shufps/0xaxe/0xaxe/0xaxe.kicad_sch

## KiCad design 0xaxe/0xaxe.kicad_sch (2024-04-14)

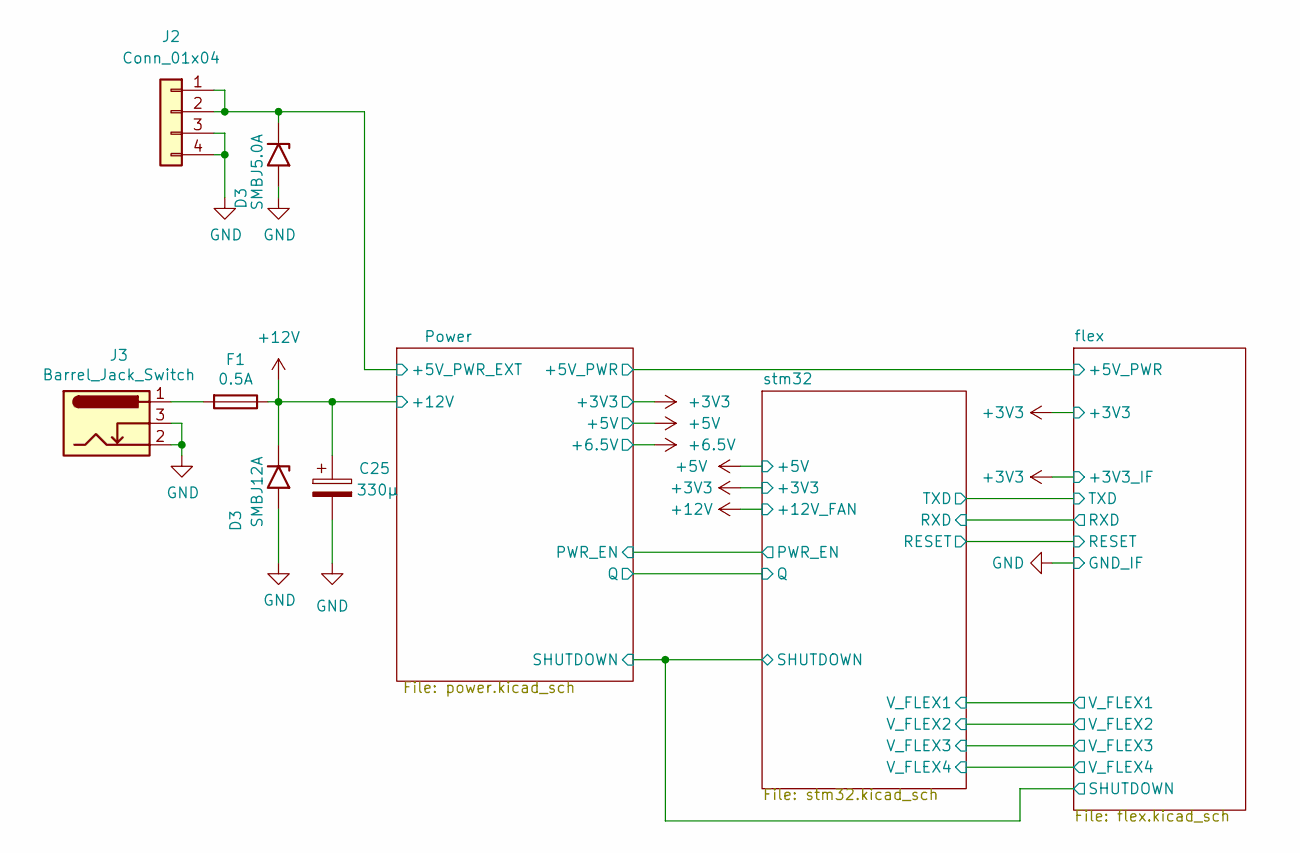
[picture p4: schematic 0xaxe.kicad_sch]

Parts:
C25: 330µ; CP_Elec_8x10
D3: SMBJ12A; D_SMB
F1: 0.5A; fuseholder_littlefuse_blok
J2: Conn_01x04; BARRIER-TERMINAL-ANYTEK-4pol
J3: Barrel_Jack_Switch; BarrelJack_CUI_PJ-102AH_Horizontal

Connections:
+5V_PWR_EXT: D3.1 (A1), J2.1, J2.2
+12V: C25.1, D3.1 (A1), F1.1
GND: C25.2, D3.2 (A2), J2.3, J2.4, J3.2, J3.3
unnamed: F1.2, J3.1
