shufps/0xaxe/0xaxe/flex1.kicad_sch

## KiCad design 0xaxe/flex1.kicad_sch (2024-04-14)

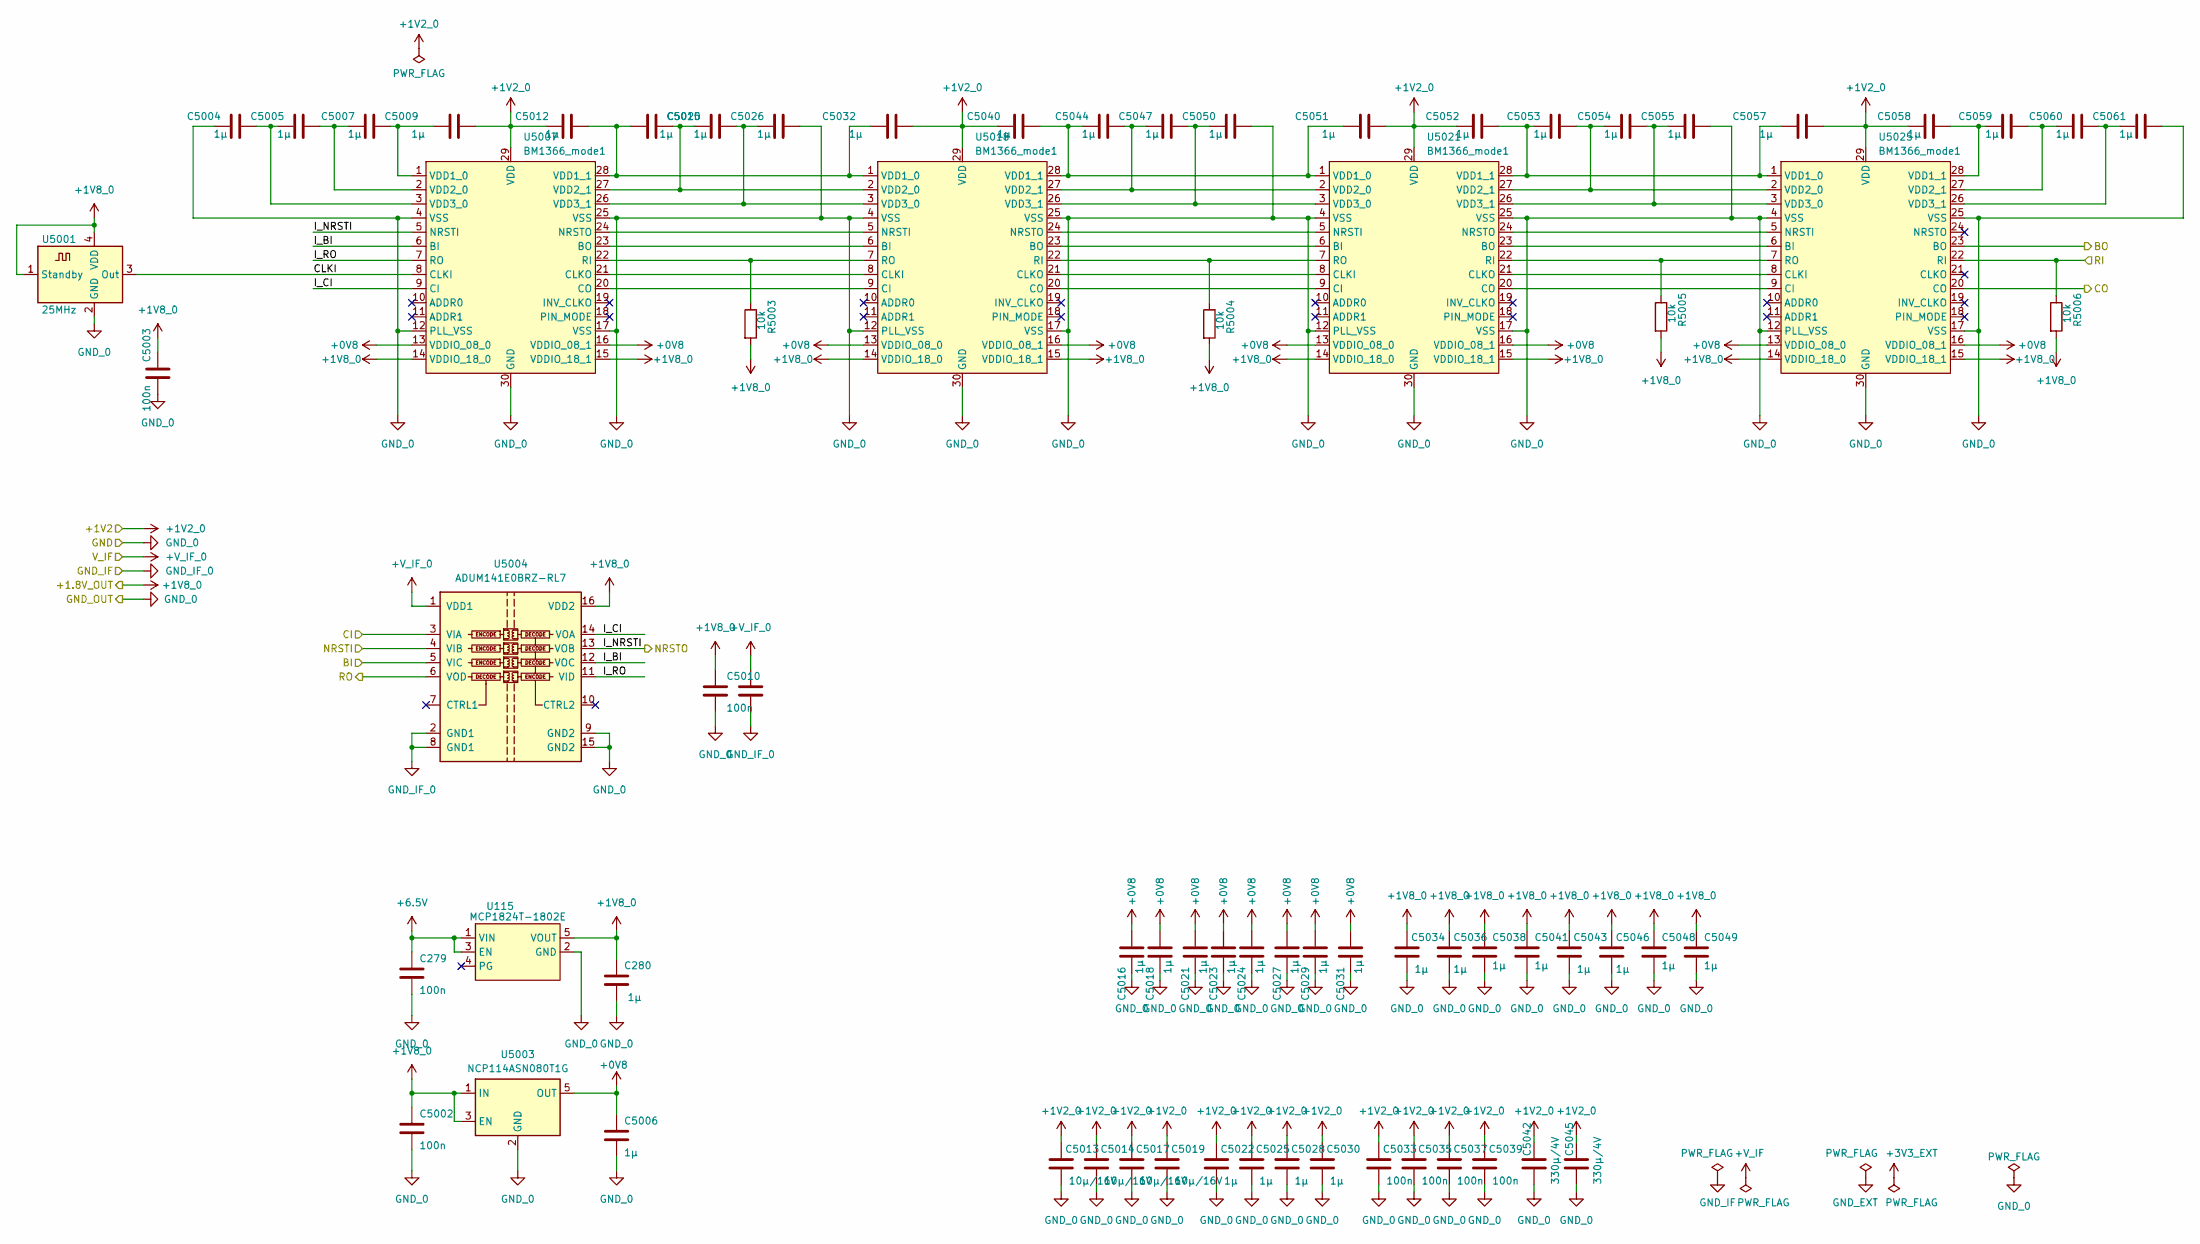
[picture p5: schematic flex1.kicad_sch]

Parts:
C279, C5002, C5003, C5010, C5011, C5033, C5035, C5037, C5039: 100n; C_0805_2012Metric
C280, C5004, C5005, C5006, C5007, C5009, C5012, C5015, C5016, C5018, C5020, C5021, C5022, C5023, C5024, C5025, C5026, C5027, C5028, C5029, C5030, C5031, C5032, C5034, C5036, C5038, C5040, C5041, C5043, C5044, C5046, C5047, C5048, C5049, C5050, C5051, C5052, C5053, C5054, C5055, C5057, C5058, C5059, C5060, C5061: 1µ; C_0805_2012Metric
C5013, C5014, C5017, C5019: 10µ/16V; C_0805_2012Metric
C5042, C5045: 330µ/4V; C_1210_3225Metric
R5003, R5004, R5005, R5006: 10k; R_0805_2012Metric
U115: MCP1824T-1802E; SOT-23-5
U5001: 25MHz; Oscillator_SMD_EuroQuartz_XO32-4Pin_3.2x2.5mm
U5003: NCP114ASN080T1G; SOT-23-5
U5004: ADUM141E0BRZ-RL7; SOIC-16_3.9x9.9mm_P1.27mm
U5005, U5006, U5008, U5009, U5010, U5011, U5012, U5013, U5014, U5015, U5016, U5017, U5019, U5020, U5022, U5024, U5026: +0V8
U5007, U5018, U5021, U5025: BM1366_mode1; BM1366

Connections:
+1V2_0: C5009.2, C5012.1, C5013.1, C5014.1, C5017.1, C5019.1, C5022.1, C5025.1, C5028.1, C5030.1, C5032.2, C5033.1, C5035.1, C5037.1, C5039.1, C5040.1, C5042.1, C5045.1, C5051.2, C5052.1, C5057.2, C5058.1, U5007.29 (VDD), U5018.29 (VDD), U5021.29 (VDD), U5025.29 (VDD)
+1V8_0: C280.1, C5002.1, C5003.1, C5010.1, C5034.1, C5036.1, C5038.1, C5041.1, C5043.1, C5046.1, C5048.1, C5049.1, R5003.2, R5004.2, R5005.2, R5006.2, U115.5 (VOUT), U5001.1 (Standby), U5001.4 (VDD), U5003.1 (IN), U5003.3 (EN), U5004.16 (VDD2), U5007.14 (VDDIO_18_0), U5007.15 (VDDIO_18_1), U5018.14 (VDDIO_18_0), U5018.15 (VDDIO_18_1), U5021.14 (VDDIO_18_0), U5021.15 (VDDIO_18_1), U5025.14 (VDDIO_18_0), U5025.15 (VDDIO_18_1)
+6.5V: C279.1, U115.1 (VIN), U115.3 (EN)
+V_IF_0: C5011.1, U5004.1 (VDD1)
BI: U5004.5 (VIC)
BO: U5025.23 (BO)
CI: U5004.3 (VIA)
CLKI: U5001.3 (Out), U5007.8 (CLKI)
CO: U5025.20 (CO)
GND_0: C279.2, C280.2, C5002.2, C5003.2, C5004.1, C5006.2, C5010.2, C5013.2, C5014.2, C5016.1, C5017.2, C5018.1, C5019.2, C5021.1, C5022.2, C5023.1, C5024.1, C5025.2, C5026.2, C5027.1, C5028.2, C5029.1, C5030.2, C5031.1, C5033.2, C5034.2, C5035.2, C5036.2, C5037.2, C5038.2, C5039.2, C5041.2, C5042.2, C5043.2, C5045.2, C5046.2, C5048.2, C5049.2, C5050.2, C5055.2, C5061.2, U115.2 (GND), U5001.2 (GND), U5003.2 (GND), U5004.9 (GND2), U5004.15 (GND2), U5007.4 (VSS), U5007.12 (PLL_VSS), U5007.17 (VSS), U5007.25 (VSS), U5007.30 (GND), U5018.4 (VSS), U5018.12 (PLL_VSS), U5018.17 (VSS), U5018.25 (VSS), U5018.30 (GND), U5021.4 (VSS), U5021.12 (PLL_VSS), U5021.17 (VSS), U5021.25 (VSS), U5021.30 (GND), U5025.4 (VSS), U5025.12 (PLL_VSS), U5025.17 (VSS), U5025.25 (VSS), U5025.30 (GND)
GND_IF_0: C5011.2, U5004.2 (GND1), U5004.8 (GND1)
I_BI: U5004.12 (VOC), U5007.6 (BI)
I_CI: U5004.14 (VOA), U5007.9 (CI)
I_NRSTI: U5004.13 (VOB), U5007.5 (NRSTI)
I_RO: U5004.11 (VID), U5007.7 (RO)
NRSTI: U5004.4 (VIB)
unnamed: C5004.2, C5005.1, U5007.3 (VDD3_0)
unnamed: C5005.2, C5007.1, U5007.2 (VDD2_0)
unnamed: C5006.1, U5003.5 (OUT), U5005.1
unnamed: C5007.2, C5009.1, U5007.1 (VDD1_0)
unnamed: C5012.2, C5015.2, C5032.1, U5007.28 (VDD1_1), U5018.1 (VDD1_0)
unnamed: C5015.1, C5020.1, U5007.27 (VDD2_1), U5018.2 (VDD2_0)
unnamed: C5016.2, U5009.1
unnamed: C5018.2, U5010.1
unnamed: C5020.2, C5026.1, U5007.26 (VDD3_1), U5018.3 (VDD3_0)
unnamed: C5021.2, U5011.1
unnamed: C5023.2, U5012.1
unnamed: C5024.2, U5013.1
unnamed: C5027.2, U5014.1
unnamed: C5029.2, U5016.1
unnamed: C5031.2, U5017.1
unnamed: C5040.2, C5044.1, C5051.1, U5018.28 (VDD1_1), U5021.1 (VDD1_0)
unnamed: C5044.2, C5047.1, U5018.27 (VDD2_1), U5021.2 (VDD2_0)
unnamed: C5047.2, C5050.1, U5018.26 (VDD3_1), U5021.3 (VDD3_0)
unnamed: C5052.2, C5053.1, C5057.1, U5021.28 (VDD1_1), U5025.1 (VDD1_0)
unnamed: C5053.2, C5054.1, U5021.27 (VDD2_1), U5025.2 (VDD2_0)
unnamed: C5054.2, C5055.1, U5021.26 (VDD3_1), U5025.3 (VDD3_0)
unnamed: C5058.2, C5059.1, U5025.28 (VDD1_1)
unnamed: C5059.2, C5060.1, U5025.27 (VDD2_1)
unnamed: C5060.2, C5061.1, U5025.26 (VDD3_1)
unnamed: R5003.1, U5007.22 (RI), U5018.7 (RO)
unnamed: R5004.1, U5018.22 (RI), U5021.7 (RO)
unnamed: R5005.1, U5021.22 (RI), U5025.7 (RO)
unnamed: U5006.1, U5007.13 (VDDIO_08_0)
unnamed: U5007.16 (VDDIO_08_1), U5008.1
unnamed: U5007.20 (CO), U5018.9 (CI)
unnamed: U5007.21 (CLKO), U5018.8 (CLKI)
unnamed: U5007.23 (BO), U5018.6 (BI)
unnamed: U5007.24 (NRSTO), U5018.5 (NRSTI)
unnamed: U5015.1, U5018.13 (VDDIO_08_0)
unnamed: U5018.16 (VDDIO_08_1), U5019.1
unnamed: U5018.20 (CO), U5021.9 (CI)
unnamed: U5018.21 (CLKO), U5021.8 (CLKI)
unnamed: U5018.23 (BO), U5021.6 (BI)
unnamed: U5018.24 (NRSTO), U5021.5 (NRSTI)
unnamed: U5020.1, U5021.13 (VDDIO_08_0)
unnamed: U5021.16 (VDDIO_08_1), U5022.1
unnamed: U5021.20 (CO), U5025.9 (CI)
unnamed: U5021.21 (CLKO), U5025.8 (CLKI)
unnamed: U5021.23 (BO), U5025.6 (BI)
unnamed: U5021.24 (NRSTO), U5025.5 (NRSTI)
unnamed: U5024.1, U5025.13 (VDDIO_08_0)
unnamed: U5025.16 (VDDIO_08_1), U5026.1
RI: R5006.1, U5025.22 (RI)
RO: U5004.6 (VOD)
