shufps/0xaxe/0xaxe/flex2.kicad_sch

## KiCad design 0xaxe/flex2.kicad_sch (2024-04-14)

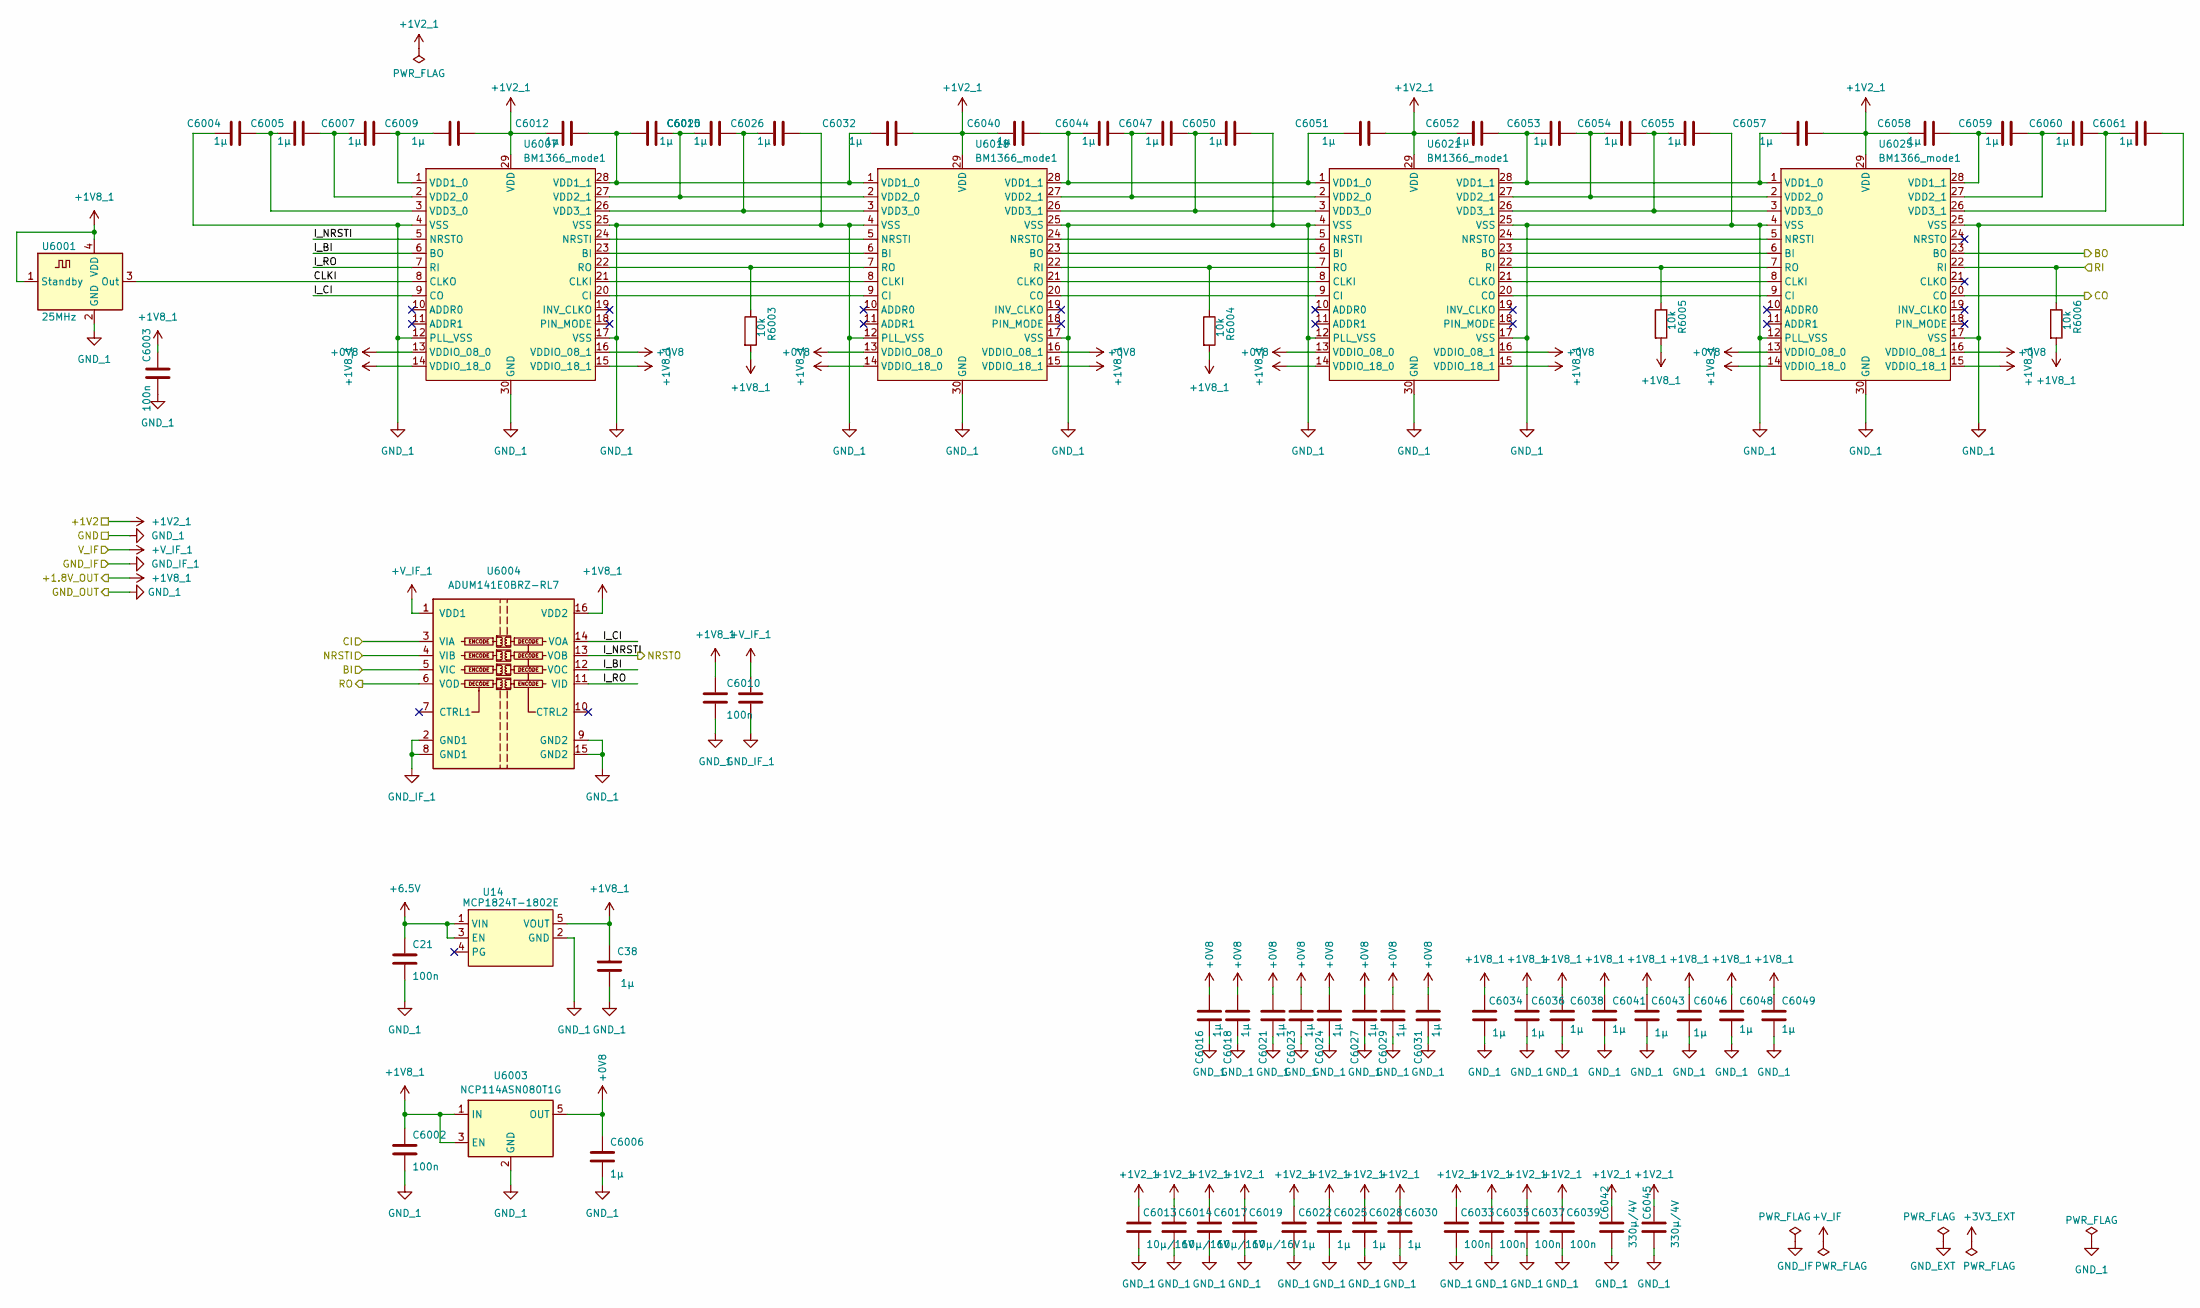
[picture p6: schematic flex2.kicad_sch]

Parts:
C21, C6002, C6003, C6010, C6011, C6033, C6035, C6037, C6039: 100n; C_0805_2012Metric
C38, C6004, C6005, C6006, C6007, C6009, C6012, C6015, C6016, C6018, C6020, C6021, C6022, C6023, C6024, C6025, C6026, C6027, C6028, C6029, C6030, C6031, C6032, C6034, C6036, C6038, C6040, C6041, C6043, C6044, C6046, C6047, C6048, C6049, C6050, C6051, C6052, C6053, C6054, C6055, C6057, C6058, C6059, C6060, C6061: 1µ; C_0805_2012Metric
C6013, C6014, C6017, C6019: 10µ/16V; C_0805_2012Metric
C6042, C6045: 330µ/4V; C_1210_3225Metric
R6003, R6004, R6005, R6006: 10k; R_0805_2012Metric
U14: MCP1824T-1802E; SOT-23-5
U6001: 25MHz; Oscillator_SMD_EuroQuartz_XO32-4Pin_3.2x2.5mm
U6003: NCP114ASN080T1G; SOT-23-5
U6004: ADUM141E0BRZ-RL7; SOIC-16_3.9x9.9mm_P1.27mm
U6005, U6006, U6008, U6009, U6010, U6011, U6012, U6013, U6014, U6015, U6016, U6017, U6019, U6020, U6022, U6024, U6026: +0V8
U6007, U6018, U6021, U6025: BM1366_mode1; BM1366

Connections:
+1V2_1: C6009.2, C6012.1, C6013.1, C6014.1, C6017.1, C6019.1, C6022.1, C6025.1, C6028.1, C6030.1, C6032.2, C6033.1, C6035.1, C6037.1, C6039.1, C6040.1, C6042.1, C6045.1, C6051.2, C6052.1, C6057.2, C6058.1, U6007.29 (VDD), U6018.29 (VDD), U6021.29 (VDD), U6025.29 (VDD)
+1V8_1: C38.1, C6002.1, C6003.1, C6010.1, C6034.1, C6036.1, C6038.1, C6041.1, C6043.1, C6046.1, C6048.1, C6049.1, R6003.2, R6004.2, R6005.2, R6006.2, U14.5 (VOUT), U6001.1 (Standby), U6001.4 (VDD), U6003.1 (IN), U6003.3 (EN), U6004.16 (VDD2), U6007.14 (VDDIO_18_0), U6007.15 (VDDIO_18_1), U6018.14 (VDDIO_18_0), U6018.15 (VDDIO_18_1), U6021.14 (VDDIO_18_0), U6021.15 (VDDIO_18_1), U6025.14 (VDDIO_18_0), U6025.15 (VDDIO_18_1)
+6.5V: C21.1, U14.1 (VIN), U14.3 (EN)
+V_IF_1: C6011.1, U6004.1 (VDD1)
BI: U6004.5 (VIC)
BO: U6025.23 (BO)
CI: U6004.3 (VIA)
CLKI: U6001.3 (Out), U6007.8 (CLKO)
CO: U6025.20 (CO)
GND_1: C21.2, C38.2, C6002.2, C6003.2, C6004.1, C6006.2, C6010.2, C6013.2, C6014.2, C6016.1, C6017.2, C6018.1, C6019.2, C6021.1, C6022.2, C6023.1, C6024.1, C6025.2, C6026.2, C6027.1, C6028.2, C6029.1, C6030.2, C6031.1, C6033.2, C6034.2, C6035.2, C6036.2, C6037.2, C6038.2, C6039.2, C6041.2, C6042.2, C6043.2, C6045.2, C6046.2, C6048.2, C6049.2, C6050.2, C6055.2, C6061.2, U14.2 (GND), U6001.2 (GND), U6003.2 (GND), U6004.9 (GND2), U6004.15 (GND2), U6007.4 (VSS), U6007.12 (PLL_VSS), U6007.17 (VSS), U6007.25 (VSS), U6007.30 (GND), U6018.4 (VSS), U6018.12 (PLL_VSS), U6018.17 (VSS), U6018.25 (VSS), U6018.30 (GND), U6021.4 (VSS), U6021.12 (PLL_VSS), U6021.17 (VSS), U6021.25 (VSS), U6021.30 (GND), U6025.4 (VSS), U6025.12 (PLL_VSS), U6025.17 (VSS), U6025.25 (VSS), U6025.30 (GND)
GND_IF_1: C6011.2, U6004.2 (GND1), U6004.8 (GND1)
I_BI: U6004.12 (VOC), U6007.6 (BO)
I_CI: U6004.14 (VOA), U6007.9 (CO)
I_NRSTI: U6004.13 (VOB), U6007.5 (NRSTO)
I_RO: U6004.11 (VID), U6007.7 (RI)
NRSTI: U6004.4 (VIB)
unnamed: C6004.2, C6005.1, U6007.3 (VDD3_0)
unnamed: C6005.2, C6007.1, U6007.2 (VDD2_0)
unnamed: C6006.1, U6003.5 (OUT), U6005.1
unnamed: C6007.2, C6009.1, U6007.1 (VDD1_0)
unnamed: C6012.2, C6015.2, C6032.1, U6007.28 (VDD1_1), U6018.1 (VDD1_0)
unnamed: C6015.1, C6020.1, U6007.27 (VDD2_1), U6018.2 (VDD2_0)
unnamed: C6016.2, U6009.1
unnamed: C6018.2, U6010.1
unnamed: C6020.2, C6026.1, U6007.26 (VDD3_1), U6018.3 (VDD3_0)
unnamed: C6021.2, U6011.1
unnamed: C6023.2, U6012.1
unnamed: C6024.2, U6013.1
unnamed: C6027.2, U6014.1
unnamed: C6029.2, U6016.1
unnamed: C6031.2, U6017.1
unnamed: C6040.2, C6044.1, C6051.1, U6018.28 (VDD1_1), U6021.1 (VDD1_0)
unnamed: C6044.2, C6047.1, U6018.27 (VDD2_1), U6021.2 (VDD2_0)
unnamed: C6047.2, C6050.1, U6018.26 (VDD3_1), U6021.3 (VDD3_0)
unnamed: C6052.2, C6053.1, C6057.1, U6021.28 (VDD1_1), U6025.1 (VDD1_0)
unnamed: C6053.2, C6054.1, U6021.27 (VDD2_1), U6025.2 (VDD2_0)
unnamed: C6054.2, C6055.1, U6021.26 (VDD3_1), U6025.3 (VDD3_0)
unnamed: C6058.2, C6059.1, U6025.28 (VDD1_1)
unnamed: C6059.2, C6060.1, U6025.27 (VDD2_1)
unnamed: C6060.2, C6061.1, U6025.26 (VDD3_1)
unnamed: R6003.1, U6007.22 (RO), U6018.7 (RO)
unnamed: R6004.1, U6018.22 (RI), U6021.7 (RO)
unnamed: R6005.1, U6021.22 (RI), U6025.7 (RO)
unnamed: U6006.1, U6007.13 (VDDIO_08_0)
unnamed: U6007.16 (VDDIO_08_1), U6008.1
unnamed: U6007.20 (CI), U6018.9 (CI)
unnamed: U6007.21 (CLKI), U6018.8 (CLKI)
unnamed: U6007.23 (BI), U6018.6 (BI)
unnamed: U6007.24 (NRSTI), U6018.5 (NRSTI)
unnamed: U6015.1, U6018.13 (VDDIO_08_0)
unnamed: U6018.16 (VDDIO_08_1), U6019.1
unnamed: U6018.20 (CO), U6021.9 (CI)
unnamed: U6018.21 (CLKO), U6021.8 (CLKI)
unnamed: U6018.23 (BO), U6021.6 (BI)
unnamed: U6018.24 (NRSTO), U6021.5 (NRSTI)
unnamed: U6020.1, U6021.13 (VDDIO_08_0)
unnamed: U6021.16 (VDDIO_08_1), U6022.1
unnamed: U6021.20 (CO), U6025.9 (CI)
unnamed: U6021.21 (CLKO), U6025.8 (CLKI)
unnamed: U6021.23 (BO), U6025.6 (BI)
unnamed: U6021.24 (NRSTO), U6025.5 (NRSTI)
unnamed: U6024.1, U6025.13 (VDDIO_08_0)
unnamed: U6025.16 (VDDIO_08_1), U6026.1
RI: R6006.1, U6025.22 (RI)
RO: U6004.6 (VOD)
