shufps/0xaxe/0xaxe/flex3.kicad_sch

## KiCad design 0xaxe/flex3.kicad_sch (2024-04-14)

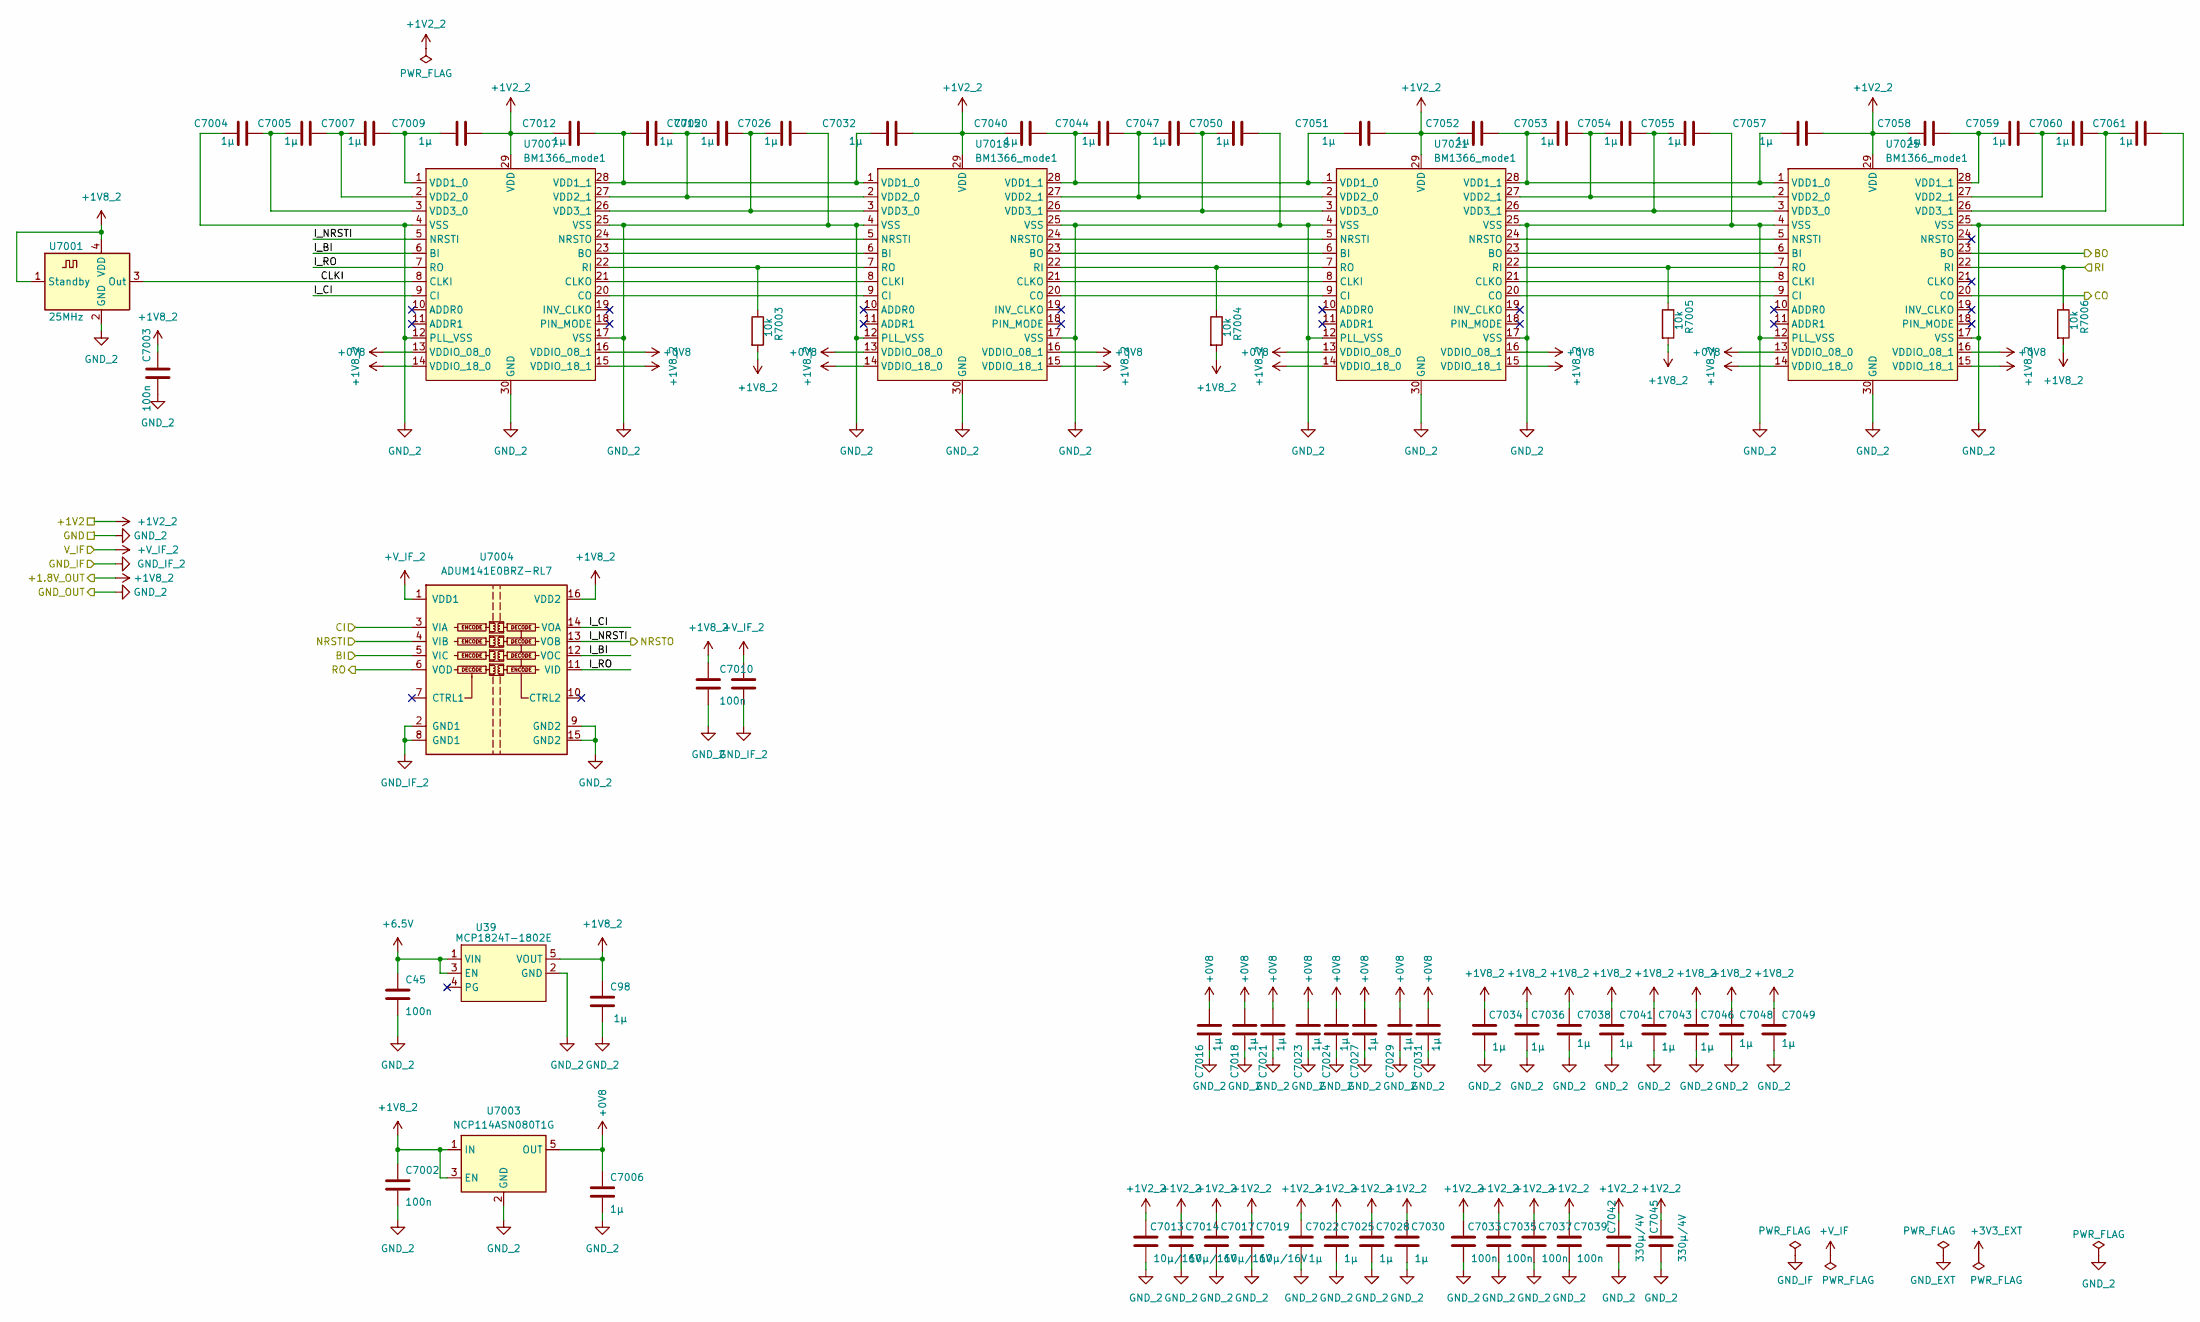
[picture p7: schematic flex3.kicad_sch]

Parts:
C45, C7002, C7003, C7010, C7011, C7033, C7035, C7037, C7039: 100n; C_0805_2012Metric
C98, C7004, C7005, C7006, C7007, C7009, C7012, C7015, C7016, C7018, C7020, C7021, C7022, C7023, C7024, C7025, C7026, C7027, C7028, C7029, C7030, C7031, C7032, C7034, C7036, C7038, C7040, C7041, C7043, C7044, C7046, C7047, C7048, C7049, C7050, C7051, C7052, C7053, C7054, C7055, C7057, C7058, C7059, C7060, C7061: 1µ; C_0805_2012Metric
C7013, C7014, C7017, C7019: 10µ/16V; C_0805_2012Metric
C7042, C7045: 330µ/4V; C_1210_3225Metric
R7003, R7004, R7005, R7006: 10k; R_0805_2012Metric
U39: MCP1824T-1802E; SOT-23-5
U7001: 25MHz; Oscillator_SMD_EuroQuartz_XO32-4Pin_3.2x2.5mm
U7003: NCP114ASN080T1G; SOT-23-5
U7004: ADUM141E0BRZ-RL7; SOIC-16_3.9x9.9mm_P1.27mm
U7005, U7006, U7008, U7009, U7010, U7011, U7012, U7013, U7014, U7015, U7016, U7017, U7019, U7020, U7022, U7024, U7026: +0V8
U7007, U7018, U7021, U7025: BM1366_mode1; BM1366

Connections:
+1V2_2: C7009.2, C7012.1, C7013.1, C7014.1, C7017.1, C7019.1, C7022.1, C7025.1, C7028.1, C7030.1, C7032.2, C7033.1, C7035.1, C7037.1, C7039.1, C7040.1, C7042.1, C7045.1, C7051.2, C7052.1, C7057.2, C7058.1, U7007.29 (VDD), U7018.29 (VDD), U7021.29 (VDD), U7025.29 (VDD)
+1V8_2: C98.1, C7002.1, C7003.1, C7010.1, C7034.1, C7036.1, C7038.1, C7041.1, C7043.1, C7046.1, C7048.1, C7049.1, R7003.2, R7004.2, R7005.2, R7006.2, U39.5 (VOUT), U7001.1 (Standby), U7001.4 (VDD), U7003.1 (IN), U7003.3 (EN), U7004.16 (VDD2), U7007.14 (VDDIO_18_0), U7007.15 (VDDIO_18_1), U7018.14 (VDDIO_18_0), U7018.15 (VDDIO_18_1), U7021.14 (VDDIO_18_0), U7021.15 (VDDIO_18_1), U7025.14 (VDDIO_18_0), U7025.15 (VDDIO_18_1)
+6.5V: C45.1, U39.1 (VIN), U39.3 (EN)
+V_IF_2: C7011.1, U7004.1 (VDD1)
BI: U7004.5 (VIC)
BO: U7025.23 (BO)
CI: U7004.3 (VIA)
CLKI: U7001.3 (Out), U7007.8 (CLKI)
CO: U7025.20 (CO)
GND_2: C45.2, C98.2, C7002.2, C7003.2, C7004.1, C7006.2, C7010.2, C7013.2, C7014.2, C7016.1, C7017.2, C7018.1, C7019.2, C7021.1, C7022.2, C7023.1, C7024.1, C7025.2, C7026.2, C7027.1, C7028.2, C7029.1, C7030.2, C7031.1, C7033.2, C7034.2, C7035.2, C7036.2, C7037.2, C7038.2, C7039.2, C7041.2, C7042.2, C7043.2, C7045.2, C7046.2, C7048.2, C7049.2, C7050.2, C7055.2, C7061.2, U39.2 (GND), U7001.2 (GND), U7003.2 (GND), U7004.9 (GND2), U7004.15 (GND2), U7007.4 (VSS), U7007.12 (PLL_VSS), U7007.17 (VSS), U7007.25 (VSS), U7007.30 (GND), U7018.4 (VSS), U7018.12 (PLL_VSS), U7018.17 (VSS), U7018.25 (VSS), U7018.30 (GND), U7021.4 (VSS), U7021.12 (PLL_VSS), U7021.17 (VSS), U7021.25 (VSS), U7021.30 (GND), U7025.4 (VSS), U7025.12 (PLL_VSS), U7025.17 (VSS), U7025.25 (VSS), U7025.30 (GND)
GND_IF_2: C7011.2, U7004.2 (GND1), U7004.8 (GND1)
I_BI: U7004.12 (VOC), U7007.6 (BI)
I_CI: U7004.14 (VOA), U7007.9 (CI)
I_NRSTI: U7004.13 (VOB), U7007.5 (NRSTI)
I_RO: U7004.11 (VID), U7007.7 (RO)
NRSTI: U7004.4 (VIB)
unnamed: C7004.2, C7005.1, U7007.3 (VDD3_0)
unnamed: C7005.2, C7007.1, U7007.2 (VDD2_0)
unnamed: C7006.1, U7003.5 (OUT), U7005.1
unnamed: C7007.2, C7009.1, U7007.1 (VDD1_0)
unnamed: C7012.2, C7015.2, C7032.1, U7007.28 (VDD1_1), U7018.1 (VDD1_0)
unnamed: C7015.1, C7020.1, U7007.27 (VDD2_1), U7018.2 (VDD2_0)
unnamed: C7016.2, U7009.1
unnamed: C7018.2, U7010.1
unnamed: C7020.2, C7026.1, U7007.26 (VDD3_1), U7018.3 (VDD3_0)
unnamed: C7021.2, U7011.1
unnamed: C7023.2, U7012.1
unnamed: C7024.2, U7013.1
unnamed: C7027.2, U7014.1
unnamed: C7029.2, U7016.1
unnamed: C7031.2, U7017.1
unnamed: C7040.2, C7044.1, C7051.1, U7018.28 (VDD1_1), U7021.1 (VDD1_0)
unnamed: C7044.2, C7047.1, U7018.27 (VDD2_1), U7021.2 (VDD2_0)
unnamed: C7047.2, C7050.1, U7018.26 (VDD3_1), U7021.3 (VDD3_0)
unnamed: C7052.2, C7053.1, C7057.1, U7021.28 (VDD1_1), U7025.1 (VDD1_0)
unnamed: C7053.2, C7054.1, U7021.27 (VDD2_1), U7025.2 (VDD2_0)
unnamed: C7054.2, C7055.1, U7021.26 (VDD3_1), U7025.3 (VDD3_0)
unnamed: C7058.2, C7059.1, U7025.28 (VDD1_1)
unnamed: C7059.2, C7060.1, U7025.27 (VDD2_1)
unnamed: C7060.2, C7061.1, U7025.26 (VDD3_1)
unnamed: R7003.1, U7007.22 (RI), U7018.7 (RO)
unnamed: R7004.1, U7018.22 (RI), U7021.7 (RO)
unnamed: R7005.1, U7021.22 (RI), U7025.7 (RO)
unnamed: U7006.1, U7007.13 (VDDIO_08_0)
unnamed: U7007.16 (VDDIO_08_1), U7008.1
unnamed: U7007.20 (CO), U7018.9 (CI)
unnamed: U7007.21 (CLKO), U7018.8 (CLKI)
unnamed: U7007.23 (BO), U7018.6 (BI)
unnamed: U7007.24 (NRSTO), U7018.5 (NRSTI)
unnamed: U7015.1, U7018.13 (VDDIO_08_0)
unnamed: U7018.16 (VDDIO_08_1), U7019.1
unnamed: U7018.20 (CO), U7021.9 (CI)
unnamed: U7018.21 (CLKO), U7021.8 (CLKI)
unnamed: U7018.23 (BO), U7021.6 (BI)
unnamed: U7018.24 (NRSTO), U7021.5 (NRSTI)
unnamed: U7020.1, U7021.13 (VDDIO_08_0)
unnamed: U7021.16 (VDDIO_08_1), U7022.1
unnamed: U7021.20 (CO), U7025.9 (CI)
unnamed: U7021.21 (CLKO), U7025.8 (CLKI)
unnamed: U7021.23 (BO), U7025.6 (BI)
unnamed: U7021.24 (NRSTO), U7025.5 (NRSTI)
unnamed: U7024.1, U7025.13 (VDDIO_08_0)
unnamed: U7025.16 (VDDIO_08_1), U7026.1
RI: R7006.1, U7025.22 (RI)
RO: U7004.6 (VOD)
