shufps/0xaxe/0xaxe/flex4.kicad_sch

## KiCad design 0xaxe/flex4.kicad_sch (2024-04-14)

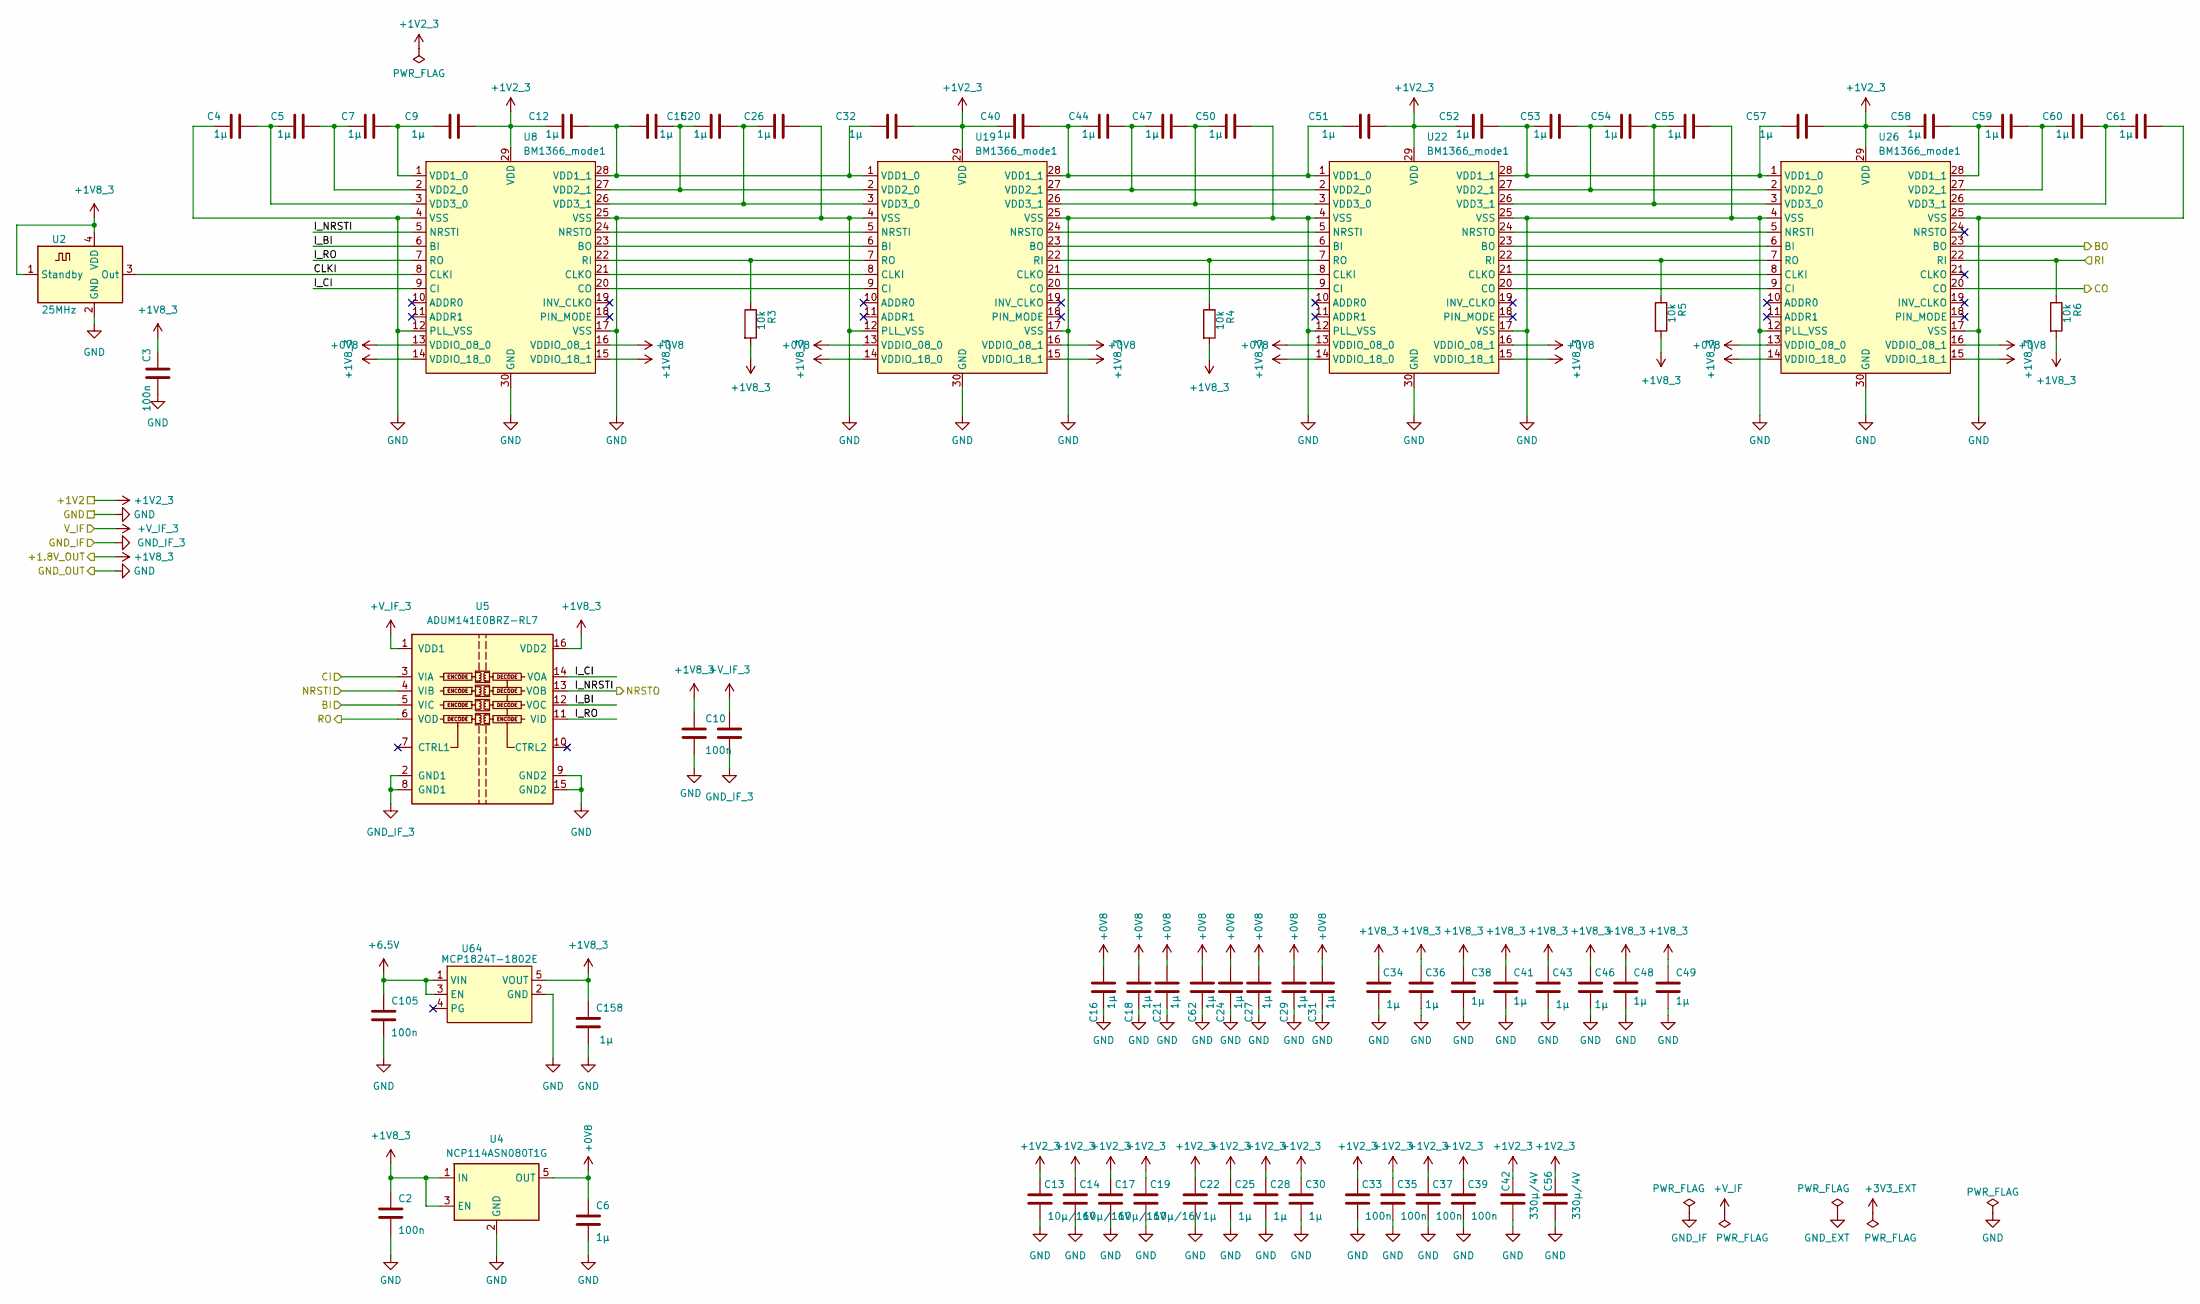
[picture p8: schematic flex4.kicad_sch]

Parts:
C2, C3, C10, C11, C33, C35, C37, C39, C105: 100n; C_0805_2012Metric
C4, C5, C6, C7, C9, C12, C15, C16, C18, C20, C21, C22, C24, C25, C26, C27, C28, C29, C30, C31, C32, C34, C36, C38, C40, C41, C43, C44, C46, C47, C48, C49, C50, C51, C52, C53, C54, C55, C57, C58, C59, C60, C61, C62, C158: 1µ; C_0805_2012Metric
C13, C14, C17, C19: 10µ/16V; C_0805_2012Metric
C42, C56: 330µ/4V; C_1210_3225Metric
R3, R4, R5, R6: 10k; R_0805_2012Metric
U2: 25MHz; Oscillator_SMD_EuroQuartz_XO32-4Pin_3.2x2.5mm
U4: NCP114ASN080T1G; SOT-23-5
U5: ADUM141E0BRZ-RL7; SOIC-16_3.9x9.9mm_P1.27mm
U6, U7, U9, U10, U11, U12, U13, U14, U15, U16, U17, U18, U20, U21, U23, U25, U27: +0V8
U8, U19, U22, U26: BM1366_mode1; BM1366
U64: MCP1824T-1802E; SOT-23-5

Connections:
+1V2_3: C9.2, C12.1, C13.1, C14.1, C17.1, C19.1, C22.1, C25.1, C28.1, C30.1, C32.2, C33.1, C35.1, C37.1, C39.1, C40.1, C42.1, C51.2, C52.1, C56.1, C57.2, C58.1, U8.29 (VDD), U19.29 (VDD), U22.29 (VDD), U26.29 (VDD)
+1V8_3: C2.1, C3.1, C10.1, C34.1, C36.1, C38.1, C41.1, C43.1, C46.1, C48.1, C49.1, C158.1, R3.2, R4.2, R5.2, R6.2, U2.1 (Standby), U2.4 (VDD), U4.1 (IN), U4.3 (EN), U5.16 (VDD2), U8.14 (VDDIO_18_0), U8.15 (VDDIO_18_1), U19.14 (VDDIO_18_0), U19.15 (VDDIO_18_1), U22.14 (VDDIO_18_0), U22.15 (VDDIO_18_1), U26.14 (VDDIO_18_0), U26.15 (VDDIO_18_1), U64.5 (VOUT)
+6.5V: C105.1, U64.1 (VIN), U64.3 (EN)
+V_IF_3: C11.1, U5.1 (VDD1)
BI: U5.5 (VIC)
BO: U26.23 (BO)
CI: U5.3 (VIA)
CLKI: U2.3 (Out), U8.8 (CLKI)
CO: U26.20 (CO)
GND: C2.2, C3.2, C4.1, C6.2, C10.2, C13.2, C14.2, C16.1, C17.2, C18.1, C19.2, C21.1, C22.2, C24.1, C25.2, C26.2, C27.1, C28.2, C29.1, C30.2, C31.1, C33.2, C34.2, C35.2, C36.2, C37.2, C38.2, C39.2, C41.2, C42.2, C43.2, C46.2, C48.2, C49.2, C50.2, C55.2, C56.2, C61.2, C62.1, C105.2, C158.2, U2.2 (GND), U4.2 (GND), U5.9 (GND2), U5.15 (GND2), U8.4 (VSS), U8.12 (PLL_VSS), U8.17 (VSS), U8.25 (VSS), U8.30 (GND), U19.4 (VSS), U19.12 (PLL_VSS), U19.17 (VSS), U19.25 (VSS), U19.30 (GND), U22.4 (VSS), U22.12 (PLL_VSS), U22.17 (VSS), U22.25 (VSS), U22.30 (GND), U26.4 (VSS), U26.12 (PLL_VSS), U26.17 (VSS), U26.25 (VSS), U26.30 (GND), U64.2 (GND)
GND_IF_3: C11.2, U5.2 (GND1), U5.8 (GND1)
I_BI: U5.12 (VOC), U8.6 (BI)
I_CI: U5.14 (VOA), U8.9 (CI)
I_NRSTI: U5.13 (VOB), U8.5 (NRSTI)
I_RO: U5.11 (VID), U8.7 (RO)
NRSTI: U5.4 (VIB)
unnamed: C4.2, C5.1, U8.3 (VDD3_0)
unnamed: C5.2, C7.1, U8.2 (VDD2_0)
unnamed: C6.1, U4.5 (OUT), U6.1
unnamed: C7.2, C9.1, U8.1 (VDD1_0)
unnamed: C12.2, C15.2, C32.1, U8.28 (VDD1_1), U19.1 (VDD1_0)
unnamed: C15.1, C20.1, U8.27 (VDD2_1), U19.2 (VDD2_0)
unnamed: C16.2, U10.1
unnamed: C18.2, U11.1
unnamed: C20.2, C26.1, U8.26 (VDD3_1), U19.3 (VDD3_0)
unnamed: C21.2, U12.1
unnamed: C24.2, U14.1
unnamed: C27.2, U15.1
unnamed: C29.2, U17.1
unnamed: C31.2, U18.1
unnamed: C40.2, C44.1, C51.1, U19.28 (VDD1_1), U22.1 (VDD1_0)
unnamed: C44.2, C47.1, U19.27 (VDD2_1), U22.2 (VDD2_0)
unnamed: C47.2, C50.1, U19.26 (VDD3_1), U22.3 (VDD3_0)
unnamed: C52.2, C53.1, C57.1, U22.28 (VDD1_1), U26.1 (VDD1_0)
unnamed: C53.2, C54.1, U22.27 (VDD2_1), U26.2 (VDD2_0)
unnamed: C54.2, C55.1, U22.26 (VDD3_1), U26.3 (VDD3_0)
unnamed: C58.2, C59.1, U26.28 (VDD1_1)
unnamed: C59.2, C60.1, U26.27 (VDD2_1)
unnamed: C60.2, C61.1, U26.26 (VDD3_1)
unnamed: C62.2, U13.1
unnamed: R3.1, U8.22 (RI), U19.7 (RO)
unnamed: R4.1, U19.22 (RI), U22.7 (RO)
unnamed: R5.1, U22.22 (RI), U26.7 (RO)
unnamed: U7.1, U8.13 (VDDIO_08_0)
unnamed: U8.16 (VDDIO_08_1), U9.1
unnamed: U16.1, U19.13 (VDDIO_08_0)
unnamed: U8.24 (NRSTO), U19.5 (NRSTI)
unnamed: U8.23 (BO), U19.6 (BI)
unnamed: U8.21 (CLKO), U19.8 (CLKI)
unnamed: U8.20 (CO), U19.9 (CI)
unnamed: U19.16 (VDDIO_08_1), U20.1
unnamed: U19.20 (CO), U22.9 (CI)
unnamed: U19.21 (CLKO), U22.8 (CLKI)
unnamed: U19.23 (BO), U22.6 (BI)
unnamed: U19.24 (NRSTO), U22.5 (NRSTI)
unnamed: U21.1, U22.13 (VDDIO_08_0)
unnamed: U22.16 (VDDIO_08_1), U23.1
unnamed: U22.20 (CO), U26.9 (CI)
unnamed: U22.21 (CLKO), U26.8 (CLKI)
unnamed: U22.23 (BO), U26.6 (BI)
unnamed: U22.24 (NRSTO), U26.5 (NRSTI)
unnamed: U25.1, U26.13 (VDDIO_08_0)
unnamed: U26.16 (VDDIO_08_1), U27.1
RI: R6.1, U26.22 (RI)
RO: U5.6 (VOD)
