shufps/0xaxe/0xaxe/flex.kicad_sch

## KiCad design 0xaxe/flex.kicad_sch (2024-04-14)

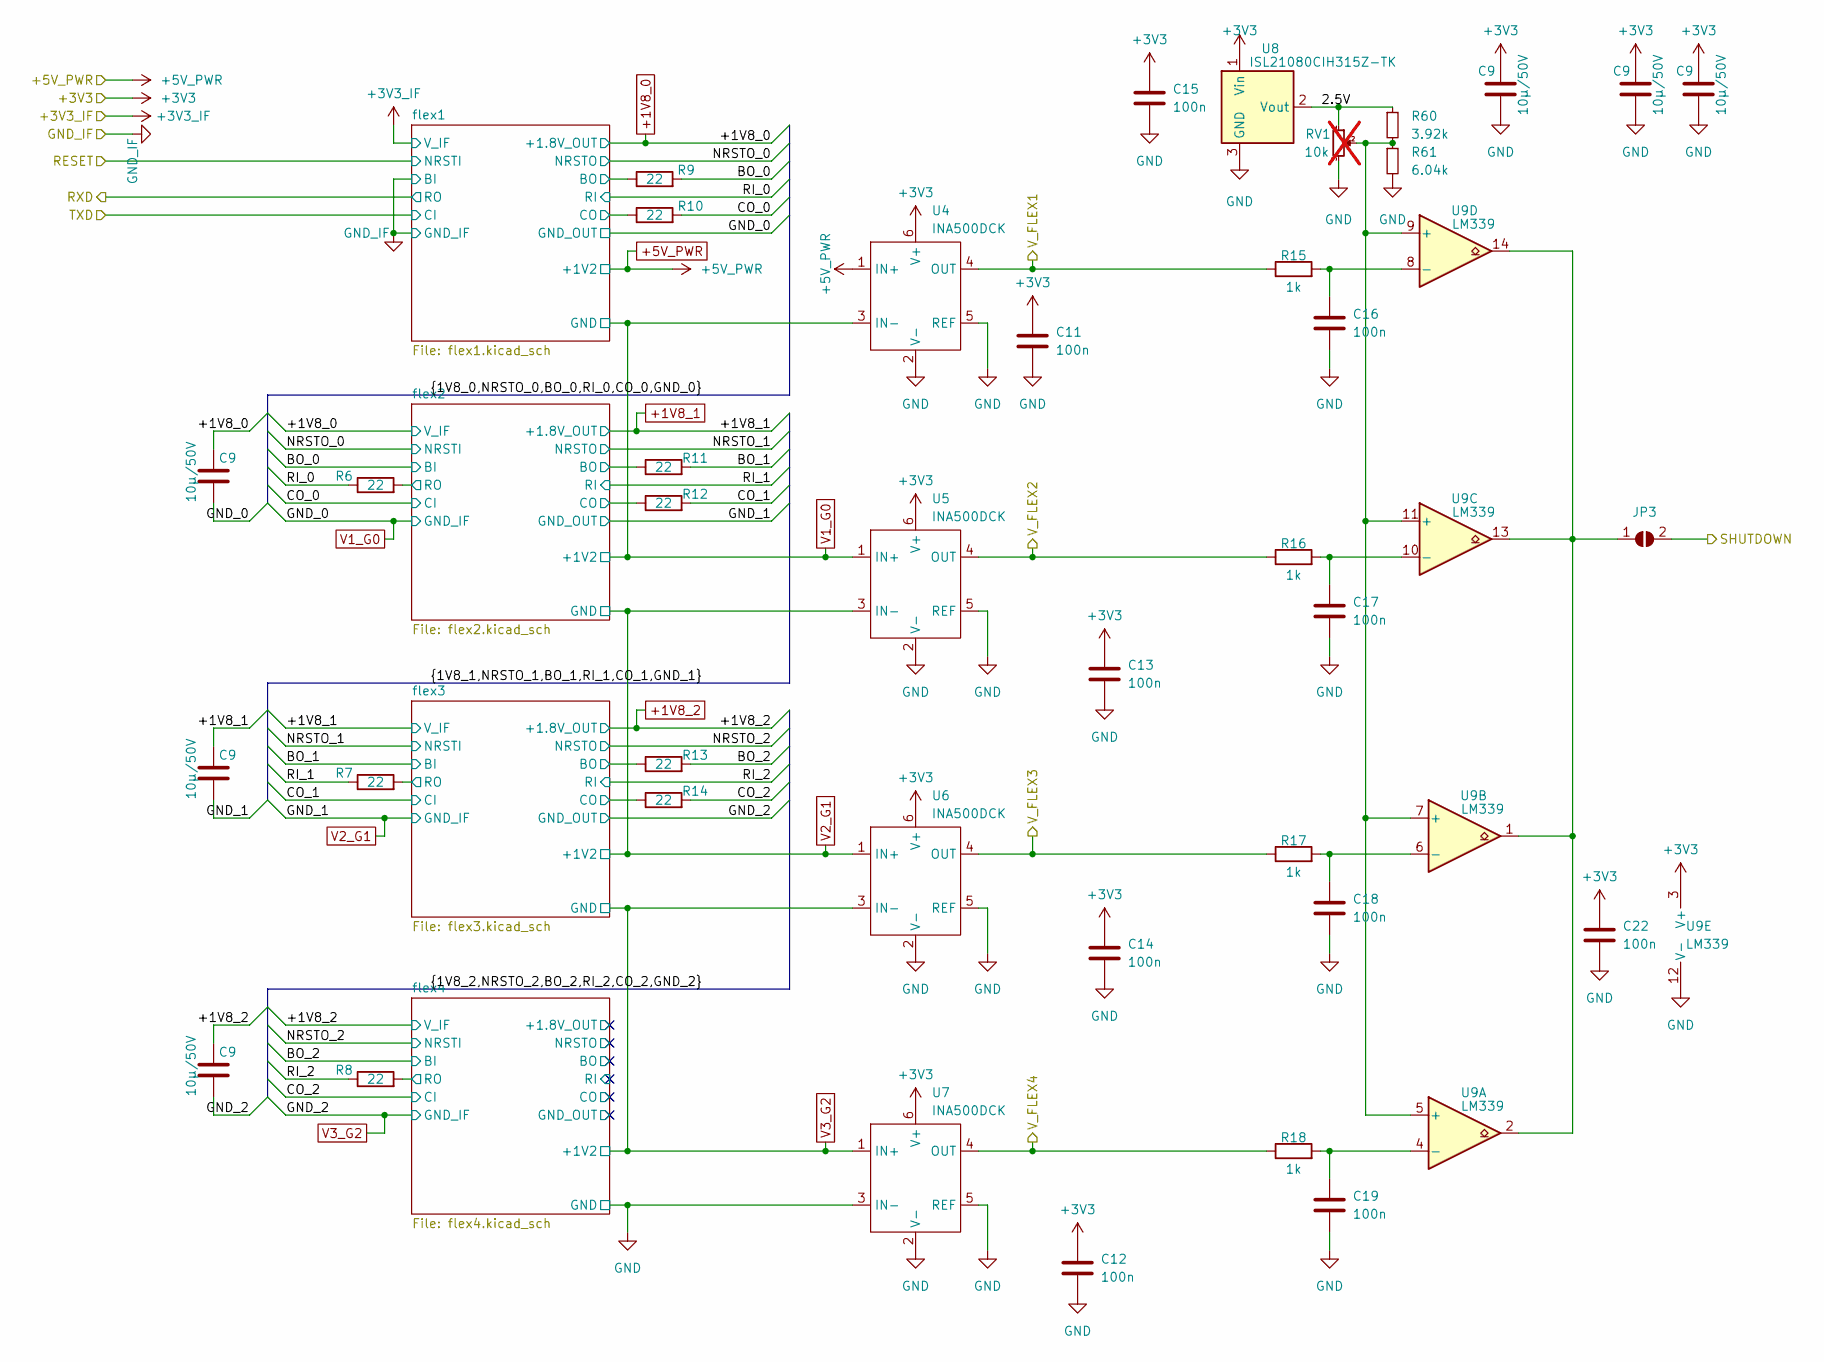
[picture p9: schematic flex.kicad_sch]

Parts:
C9: 10µ/50V; C_1206_3216Metric
C11, C12, C13, C14, C15, C16, C17, C18, C19, C22: 100n; C_0805_2012Metric
JP3: SolderJumper_2_Open; SolderJumper-2_P1.3mm_Open_RoundedPad1.0x1.5mm
R6, R7, R8, R9, R10, R11, R12, R13, R14: 22; R_0805_2012Metric
R15, R16, R17, R18: 1k; R_0805_2012Metric
R60: 3.92k; R_0805_2012Metric
R61: 6.04k; R_0805_2012Metric
RV1: 10k; Potentiometer_Bourns_3214X_Vertical; not fitted
U4, U5, U6, U7: INA500DCK; SOT-363_SC-70-6
U8: ISL21080CIH315Z-TK; SOT-23
U9: LM339; SOIC-14_3.9x8.7mm_P1.27mm

Connections:
2.5V: R60.1, RV1.1, U8.2 (Vout)
+1V8_0: C9.1
+1V8_1: C9.1
+1V8_2: C9.1
+3V3: C9.1, C11.1, C12.1, C13.1, C14.1, C15.1, C22.1, U4.6 (V+), U5.6 (V+), U6.6 (V+), U7.6 (V+), U8.1 (Vin), U9.3 (V+)
+5V_PWR: U4.1 (IN+)
BO: R9.1, R11.1, R13.1
BO_0: R9.2
BO_1: R11.2
BO_2: R13.2
CO: R10.1, R12.1, R14.1
CO_0: R10.2
CO_1: R12.2
CO_2: R14.2
GND: C9.2, C11.2, C12.2, C13.2, C14.2, C15.2, C16.2, C17.2, C18.2, C19.2, C22.2, R61.2, RV1.3, U4.2 (V-), U4.5 (REF), U5.2 (V-), U5.5 (REF), U6.2 (V-), U6.5 (REF), U7.2 (V-), U7.3 (IN-), U7.5 (REF), U8.3 (GND), U9.12 (V-)
unnamed: C16.1, R15.2, U9.8 (-)
unnamed: C17.1, R16.2, U9.10 (-)
unnamed: C18.1, R17.2, U9.6 (-)
unnamed: C19.1, R18.2, U9.4 (-)
unnamed: JP3.1 (A), U9.1, U9.2, U9.13, U9.14
unnamed: R60.2, R61.1, RV1.2, U9.5 (+), U9.7 (+), U9.9 (+), U9.11 (+)
RI_0: R6.1
RI_1: R7.1
RI_2: R8.1
RO: R6.2, R7.2, R8.2
SHUTDOWN: JP3.2 (B)
V1_G0: C9.2, U4.3 (IN-), U5.1 (IN+)
V2_G1: C9.2, U5.3 (IN-), U6.1 (IN+)
V3_G2: C9.2, U6.3 (IN-), U7.1 (IN+)
V_FLEX1: R15.1, U4.4 (OUT)
V_FLEX2: R16.1, U5.4 (OUT)
V_FLEX3: R17.1, U6.4 (OUT)
V_FLEX4: R18.1, U7.4 (OUT)
