shufps/0xaxe/0xaxe/power.kicad_sch

## KiCad design 0xaxe/power.kicad_sch (2024-04-14)

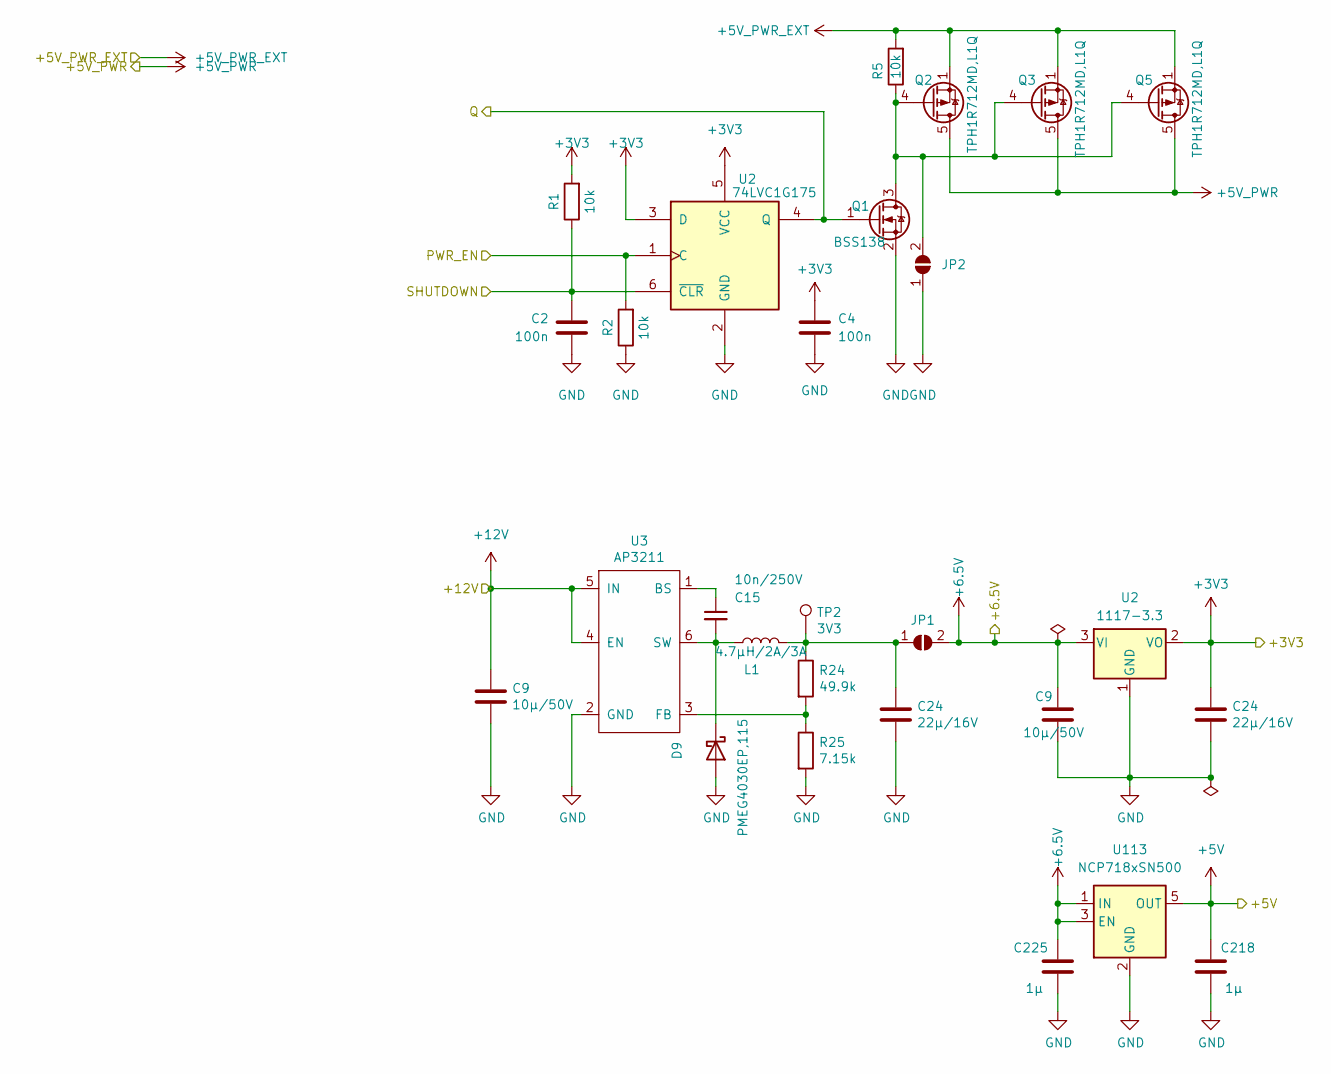
[picture p10: schematic power.kicad_sch]

Parts:
C2, C4: 100n; C_0805_2012Metric
C9: 10µ/50V; C_1206_3216Metric
C15: 10n/250V; C_0805_2012Metric
C24: 22µ/16V; C_1206_3216Metric
C218, C225: 1µ; C_0805_2012Metric
D9: PMEG4030EP,115; D_SOD-128
JP1, JP2: SolderJumper_2_Open; SolderJumper-2_P1.3mm_Open_RoundedPad1.0x1.5mm
L1: 4.7µH/2A/3A; L_Taiyo-Yuden_NR-50xx
Q1: BSS138; SOT-23
Q2, Q3, Q5: TPH1R712MD,L1Q; LFPAK56
R1, R2, R5: 10k; R_0805_2012Metric
R24: 49.9k; R_0805_2012Metric
R25: 7.15k; R_0805_2012Metric
TP2: 3V3; TestPoint_Pad_2.0x2.0mm
U2: 74LVC1G175; SOT-23-6
U3: AP3211; SOT-23-6
U113: NCP718xSN500; SOT-23-5

Connections:
+3V3: C4.1, C24.1, R1.2, U2.2 (VO), U2.3 (VI), U2.5 (VCC)
+5V: C218.1, U113.5 (OUT)
+5V_PWR: Q2.5 (D), Q3.5 (D), Q5.5 (D)
+5V_PWR_EXT: Q2.1 (S), Q2.2 (S), Q2.3 (S), Q3.1 (S), Q3.2 (S), Q3.3 (S), Q5.1 (S), Q5.2 (S), Q5.3 (S), R5.2
+6.5V: C9.1, C225.1, JP1.2 (B), U2.3 (VI), U113.1 (IN), U113.3 (EN)
+12V: C9.1, U3.4 (EN), U3.5 (IN)
GND: C2.2, C4.2, C9.2, C24.2, C218.2, C225.2, D9.2 (A), JP2.1 (A), Q1.2 (S), R2.1, R25.2, U2.1 (GND), U2.2 (VO), U3.2 (GND), U113.2 (GND)
unnamed: C15.1, U3.1 (BS)
unnamed: C15.2, D9.1 (K), L1.1, U3.6 (SW)
unnamed: C24.1, JP1.1 (A), L1.2, R24.1, TP2.1
unnamed: JP2.2 (B), Q1.3 (D), Q2.4 (G), Q3.4 (G), Q5.4 (G), R5.1
unnamed: R24.2, R25.1, U3.3 (FB)
PWR_EN: R2.2, U2.1 (GND)
Q: Q1.1 (G), U2.4 (Q)
SHUTDOWN: C2.1, R1.1, U2.6 (~CLR)
