shufps/0xaxe/0xaxe/stm32.kicad_sch

## KiCad design 0xaxe/stm32.kicad_sch (2024-04-03)

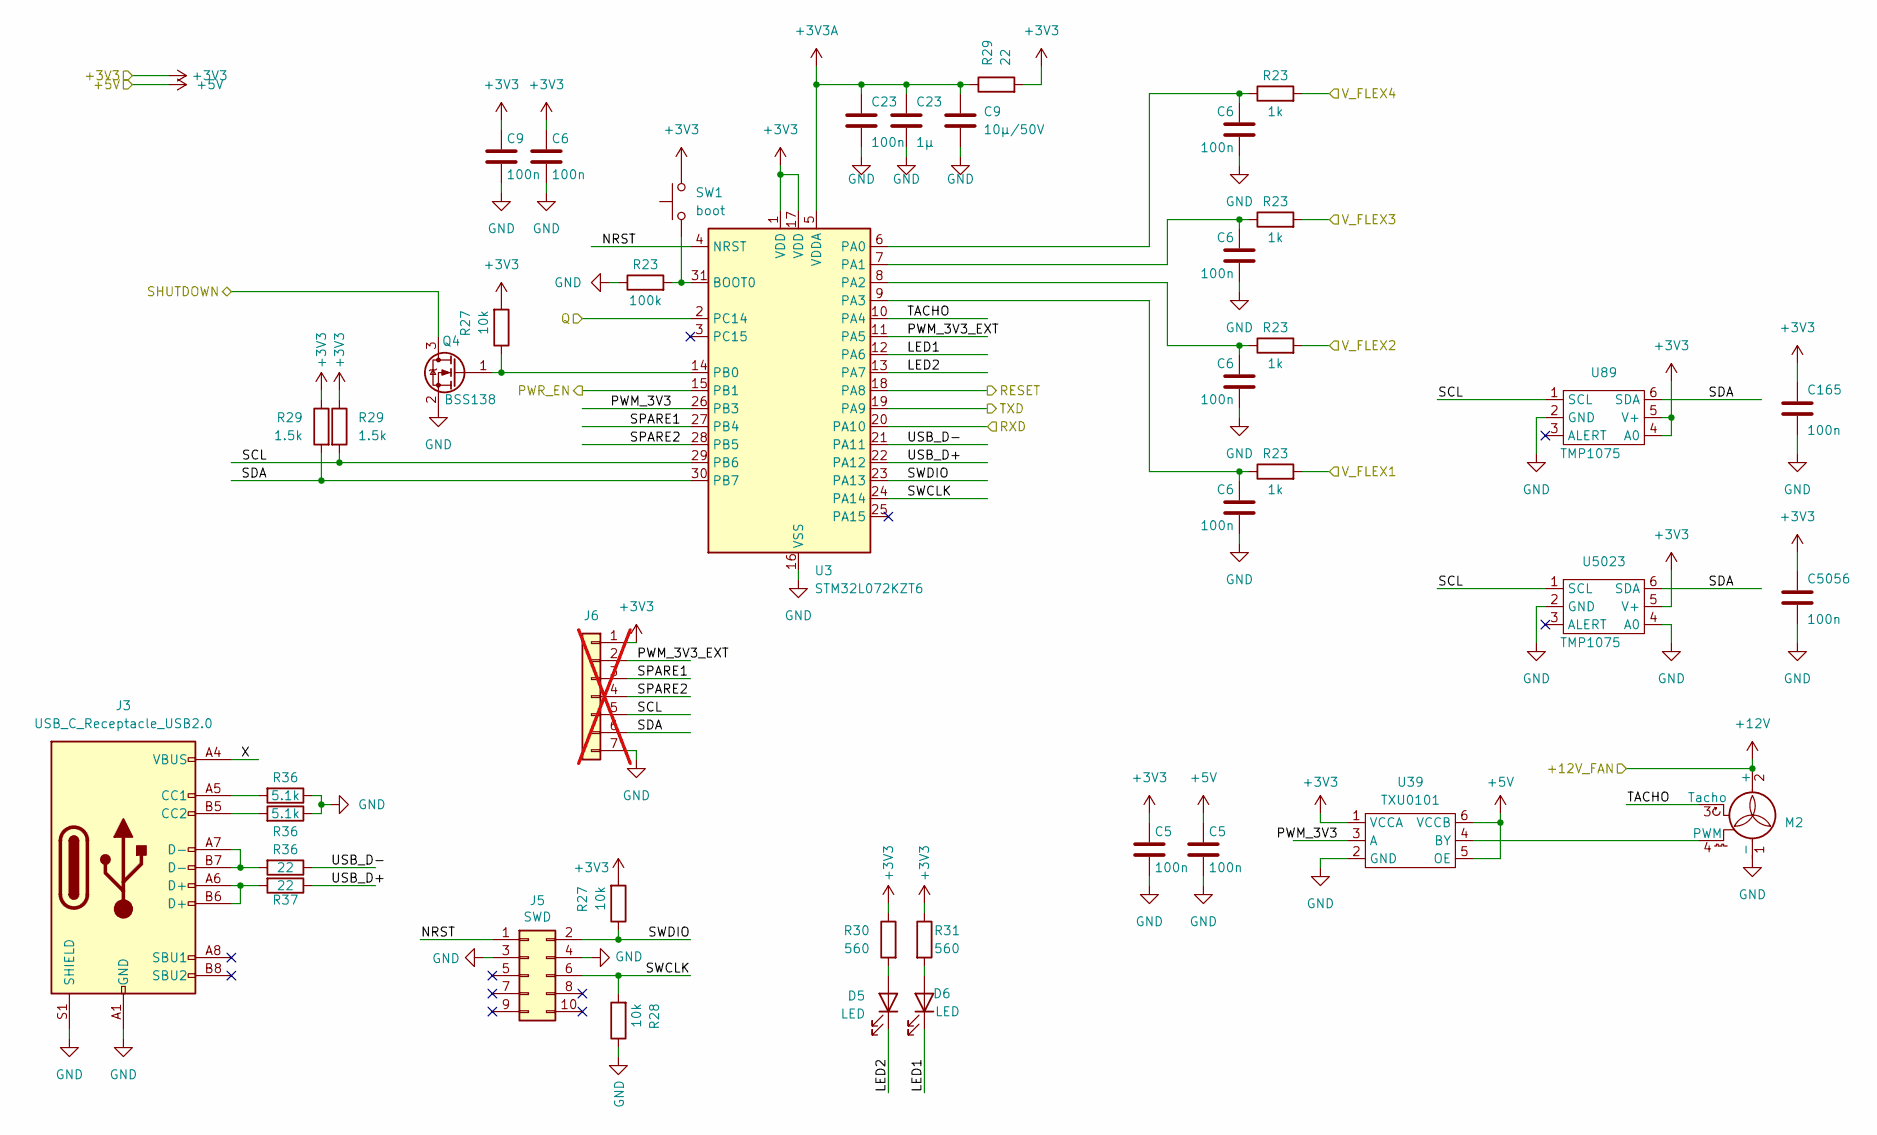
[picture p11: schematic stm32.kicad_sch]

Parts:
C5, C6, C165, C5056: 100n; C_0805_2012Metric
C9: 10µ/50V; C_1206_3216Metric
C23: 1µ; C_0805_2012Metric
D5, D6: LED; LED_1206_3216Metric
J3: USB_C_Receptacle_USB2.0; USB_C_Receptacle_GCT_USB4105-xx-A_16P_TopMnt_Horizontal
J5: SWD; PinHeader_IDC_2x05_P1.27mm_Vertical_SMD
J6: Conn_01x05; PinHeader_1x07_P2.54mm_Vertical; not fitted
M2: Fan_4pin; FanPinHeader_1x04_P2.54mm_Vertical
Q4: BSS138; SOT-23
R23: 1k; R_0805_2012Metric
R27, R28: 10k; R_0805_2012Metric
R29, R37: 22; R_0805_2012Metric
R30, R31: 560; R_0805_2012Metric
R36: 5.1k; R_0805_2012Metric
SW1: boot; SW_Push_1P1T_NO_CK_KMR2
U3: STM32L072KZT6; LQFP-32_7x7mm_P0.8mm
U39: TXU0101; SOT-363_SC-70-6
U89, U5023: TMP1075; TMP1075-DRL

Connections:
+3V3: C5.1, C6.1, C9.1, C165.1, C5056.1, J6.1, R27.2, R29.1, R29.2, R30.1, R31.1, SW1.2, U3.1 (VDD), U3.17 (VDD), U39.1 (VCCA), U89.4 (A0), U89.5 (V+), U5023.5 (V+)
+3V3A: C9.1, C23.1, R29.1, U3.5 (VDDA)
+5V: C5.1, U39.5 (OE), U39.6 (VCCB)
+12V: M2.2 (+)
GND: C5.2, C6.2, C9.2, C23.2, C165.2, C5056.2, J3.A1 (GND), J3.A12 (GND), J3.B1 (GND), J3.B12 (GND), J3.S1 (SHIELD), J5.3, J5.4, J6.7, M2.1 (-), Q4.2 (S), R23.1, R28.1, R36.1, U3.16 (VSS), U3.32 (VSS), U39.2 (GND), U89.2 (GND), U5023.2 (GND), U5023.4 (A0)
LED1: D6.1 (K), U3.12 (PA6)
LED2: D5.1 (K), U3.13 (PA7)
NRST: J5.1, U3.4 (NRST)
unnamed: C6.1, R23.1, U3.6 (PA0), U3.7 (PA1), U3.8 (PA2), U3.9 (PA3)
unnamed: D5.2 (A), R30.2
unnamed: D6.2 (A), R31.2
unnamed: J3.A5 (CC1), R36.2
unnamed: J3.A6 (D+), J3.B6 (D+), R37.2
unnamed: J3.A7 (D-), J3.B7 (D-), R36.2
unnamed: J3.B5 (CC2), R36.2
unnamed: M2.4 (PWM), U39.4 (BY)
unnamed: Q4.1 (G), R27.1, U3.14 (PB0)
unnamed: R23.2, SW1.1, U3.31 (BOOT0)
PWM_3V3: U3.26 (PB3), U39.3 (A)
PWM_3V3_EXT: J6.2, U3.11 (PA5)
PWR_EN: U3.15 (PB1)
Q: U3.2 (PC14)
RESET: U3.18 (PA8)
RXD: U3.20 (PA10)
SCL: J6.5, R29.2, U3.29 (PB6), U89.1 (SCL), U5023.1 (SCL)
SDA: J6.6, R29.2, U3.30 (PB7), U89.6 (SDA), U5023.6 (SDA)
SHUTDOWN: Q4.3 (D)
SPARE1: J6.3, U3.27 (PB4)
SPARE2: J6.4, U3.28 (PB5)
SWCLK: J5.6, R28.2, U3.24 (PA14)
SWDIO: J5.2, R27.1, U3.23 (PA13)
TACHO: M2.3 (Tacho), U3.10 (PA4)
TXD: U3.19 (PA9)
USB_D+: R37.1, U3.22 (PA12)
USB_D-: R36.1, U3.21 (PA11)
V_FLEX1: R23.2
V_FLEX2: R23.2
V_FLEX3: R23.2
V_FLEX4: R23.2
X: J3.A4 (VBUS), J3.A9 (VBUS), J3.B4 (VBUS), J3.B9 (VBUS)
